martin-77/eurobox/cad/v110/SCAD/eurobox_v110_knob.scad

$fn=96;

pitch = 2.0;
female_core_r = 3.50;
female_major_r = 4.25;
female_root_w = 1.50;
female_crest_w = 0.90;

module ridge_rh(core_r, major_r, pitch, len, root_w, crest_w, z0=0, steps=480) {
    inner_r = core_r - 0.12;
    root_half = root_w/2;
    crest_half = crest_w/2;
    a1 = 360*len/pitch;
    function ang(i)=a1*i/steps;
    function zc(i)=pitch*ang(i)/360;
    function pt(r,a,z)=[r*cos(a),r*sin(a),z];
    pts=[for(i=[0:steps]) let(a=ang(i),z=zc(i))
        each [
            pt(inner_r,a,z-root_half),
            pt(major_r,a,z-crest_half),
            pt(major_r,a,z+crest_half),
            pt(inner_r,a,z+root_half)
        ]];
    side_faces=[for(i=[0:steps-1]) for(j=[0:3]) each [
        [4*(i+1)+((j+1)%4),4*(i+1)+j,4*i+j],
        [4*i+((j+1)%4),4*(i+1)+((j+1)%4),4*i+j]
    ]];
    start_face=[[2,1,0],[3,2,0]];
    e=4*steps;
    end_face=[[e+1,e+2,e+3],[e,e+1,e+3]];
    translate([0,0,z0])
        polyhedron(points=pts,faces=concat(side_faces,start_face,end_face),convexity=100);
}

module female_thread_cutter(len,z0=0,overrun=1.0) {
    union() {
        translate([0,0,z0-overrun])
            cylinder(r=female_core_r,h=len+2*overrun);
        ridge_rh(
            female_core_r,female_major_r,pitch,
            len+2*overrun,female_root_w,female_crest_w,
            z0-overrun,ceil((len+2*overrun)/pitch*16)
        );
    }
}

module scalloped_knob(h=9.5) {
    difference() {
        cylinder(r=15,h=h);
        for(a=[0:45:315])
            translate([16.2*cos(a),16.2*sin(a),-0.2])
                cylinder(r=3.4,h=h+0.4);
    }
}

knob_h = 9.50;
cone_h = 0.70;
cone_base_d = 11.20;
cone_tip_d = 8.30;

// Closed visible top:
// thread starts only above roof_z, leaving a solid cap.
roof_z = 1.60;
total_h = knob_h + cone_h;
thread_len = total_h - roof_z + 0.10;

difference() {
    union() {
        scalloped_knob(knob_h);

        // Male self-centering cone on clamp-facing side.
        // It bears on the rotating bushing recess, not the clamp.
        translate([0,0,knob_h])
            cylinder(d1=cone_base_d,d2=cone_tip_d,h=cone_h);
    }

    // Blind RH8x2 female thread: clamp-facing end open, visible end closed.
    female_thread_cutter(thread_len,roof_z,0.40);
}
