martin-77/eurobox/scripts/check_v60_workflow_contract.py

"""Post-build contract checks for the canonical v60 build.

This file only verifies the validation report produced by the canonical geometry
stages. It does not rebuild or independently substitute thread geometry.
"""

import json

with open('build_v60/VALIDATION_v60.json', encoding='utf-8') as fh:
    core = json.load(fh)
with open('build_v60/VALIDATION_v60_full.json', encoding='utf-8') as fh:
    full = json.load(fh)

assert not core['failures'], core['failures']
assert not full['failures'], full['failures']
assert core['stage'] == 'clean_structural_core_continuous_carrier', core['stage']
assert full['stage'] == 'full_direct_mechanism_v50_box_clamp_single_source', full['stage']

assert core['datums']['clamp_spacing_mm'] == 160.0
assert full['rack']['clamp_spacing_mm'] == 160.0
assert full['base']['right_bbox_mm'][0] <= 296.0
assert full['base']['right_bbox_mm'][1] <= 275.0
assert full['base']['mirror_delta_mm3'] <= 0.0001
assert full['handed_stl_export']['byte_distinct']
assert full['handed_stl_export']['mirror_geometry_ok']
assert full['handed_stl_export']['mirror_bounds_ok']
assert full['handed_stl_export']['mirror_vertex_set_ok']

# Box clamp: one v50-style architecture only. BASE is a smooth housing;
# the removable lead-nut cartridge contains the only working female RH8x2 thread.
box = full['box_clamp']
assert box['architecture'] == 'v50_direct_removable_lead_nut_cartridge_local_holm_stations', box
assert box['integral_female_threads'] is False, box
assert box['base_has_working_thread'] is False, box
assert box['working_female_thread_location'] == 'removable_lead_nut_cartridge', box
expected_spindles = core['datums']['box_clamp_spindle_x_mm']
assert box['spindle_x_mm'] == expected_spindles, box
assert abs(box['spindle_spacing_mm'] - (expected_spindles[1] - expected_spindles[0])) <= 1e-9, box
assert box['plate_x_mm'] == core['datums']['box_clamp_plate_x_mm'], box
assert box['plate_width_mm'] > 160.0, box
assert box['plate_travel_mm'] == 5.5, box
assert box['effective_total_width_mm'] <= 600.02, box
assert abs(box['spindle_z_mm'] - 24.54) <= 1e-9, box

lig = full['base']['carrier_spindle_ligaments']
assert lig['carrier_z0_mm'] == 9.54, lig
assert lig['carrier_z1_mm'] == 39.54, lig
assert abs(lig['lower_ligament_mm'] - lig['upper_ligament_mm']) <= 1e-9, lig
assert lig['lower_ligament_mm'] >= 9.0, lig

wall = full['base']['carrier_wall_material_checks']
assert len(wall) == 2, wall
for q in wall:
    assert q['corridor_centre_void'] is True, q
    assert [p['sample'] for p in q['samples']] == ['lower_outer','lower_inner','upper_inner','upper_outer'], q
    assert all(p['solid'] for p in q['samples']), q

station = full['base']['holm_station_checks']
assert len(station) == 2, station
assert all(abs(q['boss_to_holm_gap_mm'] - 24.0) <= 1e-9 for q in station), station
assert all(q['knob_to_holm_clearance_mm'] >= 20.0 for q in station), station

plate_lig = full['base']['plate_counterbore_ligaments']
assert abs(plate_lig['lower_ligament_mm'] - plate_lig['upper_ligament_mm']) <= 1e-9, plate_lig
assert plate_lig['lower_ligament_mm'] >= 9.0, plate_lig
assert len(box['cartridge_insertion']) == 10, box
assert all(q['base_common_mm3'] <= 0.0001 for q in box['cartridge_insertion']), box['cartridge_insertion']
assert set(q['lift_mm'] for q in box['cartridge_insertion']) == {20.0,10.0,5.0,2.0,0.0}, box['cartridge_insertion']

top_closure = full['base']['lead_nut_top_closure_checks']
assert len(top_closure) == 2, top_closure
for q in top_closure:
    assert abs(q['carrier_cap_top_z_mm'] - q['base_top_z_mm']) <= 1e-9, q
    assert len(q['samples']) == 9, q
    assert all(p['assembled_solid'] for p in q['samples']), q
    assert all(p['carrier_solid'] for p in q['samples']), q
    assert q['pin_recess_open'] is True, q
    assert 3.6 <= q['allowed_pin_recess_width_mm'] <= 4.0, q

guide_clear = full['base']['obsolete_guide_clearance_checks']
assert len(guide_clear) == 2, guide_clear
for q in guide_clear:
    assert len(q['samples']) == 2, q
    assert all(not p['solid'] for p in q['samples']), q

pin_cradles = full['base']['lead_nut_pin_wall_checks']
assert len(pin_cradles) == 2, pin_cradles
for q in pin_cradles:
    assert q['mode'] == 'round top-open U-cradle', q
    assert len(q['samples']) == 10, q
    for p in q['samples']:
        assert p['solid'] == p['expected_solid'], p

printability = box['lead_nut_printability']
assert printability['body_profile'] == 'true R8 lower semicircle', printability
assert abs(printability['semicircle_radius_mm'] - 8.0) <= 1e-9, printability
assert abs(printability['body_full_width_mm'] - 16.0) <= 1e-9, printability
assert printability['base_pocket_floor_bridge_mm'] <= 0.5, printability
assert printability['pin_cradle'] == 'round Ø3.4 top-open U-cradle', printability
assert printability['upper_body'] == 'closed except functional cross-pin bore/top-entry throat', printability
gap = printability['upper_gap_checks']
assert len(gap) == 6, gap
assert all(q['solid'] == q['expected_solid'] for q in gap), gap
assert {q['sample'] for q in gap if not q['solid']} == {'pin-axis','pin-top-entry'}, gap
assert printability['preferred_print_orientation'] == 'rotate -90deg about X; RH8x2 axis vertical', printability
span = printability['closing_span_samples']
assert [q['local_z_mm'] for q in span] == [0.0,-2.0,-4.0,-6.0,-8.0], span
assert all(span[i]['pocket_width_mm'] > span[i+1]['pocket_width_mm'] for i in range(len(span)-1)), span
assert span[-1]['pocket_width_mm'] <= 0.5, span

pin_drop = full['base']['lead_nut_pin_top_insertion']
assert len(pin_drop) == 2, pin_drop
assert all(abs(q['pin_axis_z_mm'] - 34.54) <= 1e-9 for q in pin_drop), pin_drop
for q in pin_drop:
    assert len(q['path']) == 5, q
    assert all(p['base_common_mm3'] <= 0.0001 for p in q['path']), q
    assert all(p['lead_nut_common_mm3'] <= 0.0001 for p in q['path']), q

assert box['final_assembly_replaceable_module_count'] == 0, box
assert box['final_assembly_contains_separate_lead_nut_hardware'] is True, box
assert box['final_assembly_lead_nut_cartridge_count'] == 4, box
assert box['final_assembly_lead_nut_pin_count'] == 4, box
assert box['final_assembly_lead_nut_clip_count'] == 4, box
assert box['final_assembly_box_clamp_knob_count'] == 4, box
assert box['final_assembly_knob_retainer_count'] == 4, box
assert box['final_assembly_plate_retainer_clip_count'] == 4, box
assert box['final_assembly_installed_spindle_x_mm'] == expected_spindles, box
assert all(q['base_common_mm3'] <= 0.0001 for q in box['thread_motion']), box['thread_motion']
assert box['thread_brep_common_tolerance_mm3'] == 1.20, box
assert all(q['cartridge_common_mm3'] <= box['thread_brep_common_tolerance_mm3'] for q in box['thread_motion']), box['thread_motion']

# Lead screw must be the exact closed printable CGAL mesh. The 7 mm knob
# drive now starts with a support-free hex frustum and retains 5 mm full AF10.
ls = box['lead_screw']
assert ls['knob_hex_length_mm'] == ls['knob_thickness_mm'] == 7.0, ls
assert ls['full_hex_drive_length_mm'] >= 5.0, ls
assert abs(ls['hex_taper_length_mm'] - 2.0) <= 1e-9, ls
assert ls['mesh_topology']['boundary_edges'] == 0, ls
assert ls['mesh_topology']['nonmanifold_edges'] == 0, ls
assert len(ls['main_thread_samples']) == 8, ls
assert all(q['ridge_center_solid'] for q in ls['main_thread_samples']), ls
assert all(not q['between_turns_solid'] for q in ls['main_thread_samples']), ls

lsp = box['lead_screw_printability']
assert lsp['preferred_print_orientation'] == 'vertical on outer-stud pilot; screw axis +Z', lsp
assert abs(lsp['flat_pilot_d_mm'] - 6.5) <= 1e-9, lsp
assert abs(lsp['flat_pilot_h_mm'] - 0.8) <= 1e-9, lsp
assert lsp['outer_thread_usable_mm'] >= 6.0, lsp
assert abs(lsp['hex_taper_h_mm'] - 2.0) <= 1e-9, lsp
assert lsp['full_hex_drive_h_mm'] >= 5.0, lsp
assert lsp['shoulder_taper_max_slope_dr_dz'] <= 1.0, lsp
assert lsp['plate_matching_conical_seat'] is True, lsp
assert lsp['knob_matching_hex_frustum'] is True, lsp

pr = box['plate_spindle_retention']
assert pr['clip_count_final_assembly'] == 4, pr
assert len(pr['checks']) == 2, pr
assert all(q['spindle_common_mm3'] <= 0.0001 for q in pr['checks']), pr
assert all(q['plate_common_mm3'] <= 0.0001 for q in pr['checks']), pr
assert pr['service_channel_width_mm'] >= 11.2, pr
assert pr['service_channel_depth_mm'] == 2.0, pr
assert len(pr['clip_insertion_path']) == 10, pr
assert all(q['plate_common_mm3'] <= 0.00001 for q in pr['clip_insertion_path']), pr

ms = box['mounting_sequence']
assert ms['order'] == [
    'lead_nut_insert_from_top',
    'lead_nut_cross_pin',
    'lead_nut_pin_clip',
    'lead_screw_through_plate',
    'plate_retainer_clip_via_bottom_service_channel',
    'plate_spindle_subassembly_threaded_into_fixed_lead_nut',
    'knob_on_tapered_7mm_hex_with_5mm_full_drive',
    'knob_retainer_nut_on_outer_RH8x2_stud',
], ms
assert len(ms['lead_nut_top_insertion']) == 10, ms
assert all(q['base_common_mm3'] <= 0.0001 for q in ms['lead_nut_top_insertion']), ms
assert len(ms['lead_nut_pin_top_insertion']) == 2, ms
for q in ms['lead_nut_pin_top_insertion']:
    assert len(q['path']) == 5, q
    assert all(p['base_common_mm3'] <= 0.0001 for p in q['path']), q
    assert all(p['lead_nut_common_mm3'] <= 0.0001 for p in q['path']), q
assert len(ms['threaded_plate_approach']) == 10, ms
assert all(q['plate_base_common_mm3'] <= 0.0001 for q in ms['threaded_plate_approach']), ms
assert all(q['spindle_base_common_mm3'] <= 0.0001 for q in ms['threaded_plate_approach']), ms
assert all(q['spindle_lead_nut_common_mm3'] <= box['thread_brep_common_tolerance_mm3'] for q in ms['threaded_plate_approach']), ms
assert all(q['knob_base_common_mm3'] <= 0.0001 for q in ms['threaded_plate_approach']), ms
assert all(q['knob_retainer_base_common_mm3'] <= 0.0001 for q in ms['threaded_plate_approach']), ms
assert len(ms['operating_knob_clearance']) == 14, ms
assert all(q['knob_base_common_mm3'] <= 0.0001 for q in ms['operating_knob_clearance']), ms
assert all(q['retainer_base_common_mm3'] <= 0.0001 for q in ms['operating_knob_clearance']), ms

# The removable lead-nut wear cartridge must contain a real printable RH8x2
# female helix.  Direct final-part samples prevent a smooth cylindrical bore
# from ever satisfying the workflow contract again.
ln = box['lead_nut_thread']
assert ln['standard'] == 'RH8x2 true radial/axial printable matched pair', ln
assert ln['pitch_mm'] == 2.0, ln
assert ln['male_major_d_mm'] == 8.0, ln
assert ln['male_crest_width_mm'] >= 0.50, ln
assert ln['female_crest_material_between_turns_mm'] >= 0.45, ln
assert ln['radial_thread_engagement_mm'] >= 0.40, ln
assert len(ln['samples']) == 8, ln
assert all(not q['groove_center_solid'] for q in ln['samples']), ln
assert all(q['between_turns_solid'] for q in ln['samples']), ln
assert ln['validated_export_part'] == 'eurobox_v60_lead_nut', ln

# The separate box-clamp knob retainer must contain a real printable RH8x2
# female helix, matched to the actual outer stud on the exported lead screw.
kr = box['knob_retainer_thread']
assert kr['standard'] == 'RH8x2 true radial/axial printable pair', kr
assert kr['pitch_mm'] == 2.0, kr
assert kr['male_major_d_mm'] == 8.0, kr
assert kr['male_crest_width_mm'] >= 0.50, kr
assert kr['female_crest_material_between_turns_mm'] >= 0.45, kr
assert kr['radial_core_clearance_mm'] >= 0.20, kr
assert kr['radial_major_clearance_mm'] >= 0.20, kr
assert len(kr['samples']) == 4, kr
assert all(q['male_ridge_center_solid'] for q in kr['samples']), kr
assert all(not q['male_between_turns_solid'] for q in kr['samples']), kr
assert all(not q['female_groove_center_solid'] for q in kr['samples']), kr
assert all(q['female_between_turns_solid'] for q in kr['samples']), kr
assert kr['validated_export_part'] == 'eurobox_v60_knob_retainer_nut', kr

# Rack retainer: one final printable 12x3 pair only.  The contract checks the
# actual radial/axial profile dimensions and direct point samples from the final
# BASE/retainer, rather than expensive whole-body phase booleans.
rlp = full['rack']['lower_printability']
assert rlp['mechanical_geometry'] == 'proven Lower shell unchanged; closure tongue extended downward only', rlp
assert rlp['print_orientation'] == 'natural Z-up on common shell/tongue floor', rlp
assert abs(rlp['common_floor_z_mm'] + 14.5) <= 1e-9, rlp
assert rlp['common_floor_material_fraction'] >= 0.995, rlp
assert rlp['saddle_under_material_mm'] >= 8.3, rlp
assert rlp['rack_saddle'] == 'upward-open semicircular seat', rlp
assert rlp['pivot_pin_bore'] == 'small horizontal round self-closing opening', rlp
pf = rlp['pivot_print_feet']
assert pf['z_mm'] == [-14.5,-10.3], pf
assert pf['y_mm'] == [-17.0,-4.0], pf
assert abs(pf['ear_thickness_mm'] - 4.6) <= 1e-9, pf
assert rlp['m4_clearance'] == 'vertical', rlp
assert abs(rlp['m4_clearance_d_mm'] - 5.0) <= 1e-9, rlp
assert rlp['functional_round_pivot_bore_preserved'] is True, rlp

closure = full['rack']['m4_closure']
assert closure['carrier_bottom_plane_z_mm'] == 9.54, closure
assert closure['carrier_top_plane_z_mm'] == 39.54, closure
assert closure['lower_closure_thickness_mm'] == 13.0, closure
assert closure['lower_closure_z_mm'] == [-14.5,-1.5], closure
assert closure['lower_shell_floor_z_mm'] == -14.5, closure
assert closure['lower_saddle_under_material_mm'] >= 8.3, closure
assert closure['upper_nut_pocket_af_mm'] == 6.9, closure
assert closure['upper_nut_pocket_z_mm'] == [5.4,9.0], closure
assert closure['upper_nut_floor_z_mm'] == 3.4, closure
assert closure['upper_nut_floor_thickness_mm'] >= 2.0, closure
assert closure['upper_nut_floor_screw_clear_d_mm'] <= 4.6, closure
assert closure['upper_nut_floor_radial_ligament_mm'] >= 1.15, closure
assert closure['upper_nut_floor_material_fraction'] >= 0.985, closure
assert closure['knob_plastic_web_mm'] == 3.2, closure
assert closure['usable_screw_length_above_knob_mm'] == 23.6, closure
assert closure['calculated_screw_tip_z_mm'] == 9.1, closure
assert closure['full_nut_screw_overrun_margin_mm'] >= 0.49, closure
assert closure['screw_length_mm'] == 30.0, closure
assert closure['retainer_pitch_mm'] == 3.0, closure
assert closure['retainer_length_mm'] >= 28.0, closure
assert closure['retainer_male_major_d_mm'] == 12.0, closure
assert closure['retainer_female_major_d_mm'] >= 12.5, closure
assert closure['retainer_thread_profile_generator'] == 'true_radial_axial_OCC_fused', closure
assert closure['entry_clear_d_mm'] >= closure['retainer_male_major_d_mm'] + 0.8, closure
assert 0.35 <= closure['entry_clear_depth_mm'] <= 0.60, closure
assert closure['female_thread_start_recess_mm'] <= 0.60, closure
assert len(closure['female_thread_removed_mm3']) == 2, closure
assert all(v >= 8.0 for v in closure['female_thread_removed_mm3']), closure
assert closure['lower_transition_shape'] == 'shallow_conical_flare', closure
assert closure['lower_transition_z_mm'] == [9.0,11.0], closure
assert closure['lower_transition_d_mm'] == [8.1,10.5], closure

ltw = closure['lower_transition_witness']
assert len(ltw) == 2, ltw
for q in ltw:
    assert len(q['samples']) == 3, q
    assert all(not s['inner_probe_solid'] for s in q['samples']), q
    assert all(s['outer_probe_solid'] for s in q['samples']), q

nhw = closure['nut_hex_capture_witness']
assert len(nhw) == 2, nhw
for q in nhw:
    assert len(q['samples']) == 3, q
    assert all(s['inner_hex_point_void'] for s in q['samples']), q
    assert all(s['outer_flat_wall_solid'] for s in q['samples']), q

p = closure['thread_printability']
assert p['pitch_mm'] == 3.0, p
assert p['male_crest_width_mm'] >= 0.70, p
assert p['female_crest_material_between_turns_mm'] >= 0.80, p
assert 9.0 <= p['approx_full_turns'] <= 10.0, p
assert p['radial_core_clearance_mm'] >= 0.20, p
assert p['radial_major_clearance_mm'] >= 0.20, p
assert p['axial_root_clearance_mm'] >= 0.25, p
assert p['axial_crest_clearance_mm'] >= 0.25, p
assert p['target_nozzle_mm'] == 0.4, p
mn = p['male_nose_transition']
assert mn['shape'] == 'shallow_conical_flare', mn
assert mn['z_local_mm'] == [-2.0,0.0], mn
assert mn['diameter_mm'] == [7.6,10.0], mn
assert abs(mn['radial_per_vertical_slope'] - 0.6) <= 1e-9, mn
lt = p['lower_transition']
assert lt['shape'] == 'shallow_conical_flare', lt
assert lt['z_mm'] == [9.0,11.0], lt
assert lt['diameter_mm'] == [8.1,10.5], lt
assert abs(lt['height_mm'] - 2.0) <= 1e-9, lt
assert abs(lt['radial_per_vertical_slope'] - 0.6) <= 1e-9, lt
assert abs(lt['female_cylindrical_bore_starts_z_mm'] - 11.0) <= 1e-9, lt

mouth = closure['female_helical_witness']
assert len(mouth) == 2, mouth
assert all(q['blocked_sample_points'] == 0 for q in mouth), mouth

female_samples = closure['female_thread_point_samples']
assert len(female_samples) == 16, female_samples
assert all(not q['groove_center_solid'] for q in female_samples), female_samples
assert all(q['between_turns_solid'] for q in female_samples), female_samples

male_samples = closure['male_thread_point_samples']
assert len(male_samples) == 8, male_samples
assert all(q['ridge_center_solid'] for q in male_samples), male_samples
assert all(not q['between_turns_solid'] for q in male_samples), male_samples

cc = core['geometry']['continuous_carrier']
assert cc['material_fraction'] >= 0.995, cc
assert cc['rack_tube_common_mm3'] <= 0.0001, cc
# Front holm no longer overlaps the carrier directly; the intentional load
# path is carrier -> full-depth straight root -> holm.
assert cc['front_holm_direct_carrier_common_mm3'] <= 0.000001, cc
assert cc['rear_holm_common_mm3'] >= 100.0, cc
assert cc['backstop_common_mm3'] >= 100.0, cc
fr = cc['front_holm_root_tie']
assert fr['section'] == 'full_carrier_depth_straight_hollow_root_with_side_twin_and_center_webs', fr
assert fr['x_mm'] == [-96.0,-64.0], fr
assert fr['carrier_y_mm'] == [-8.0,26.0], fr
assert abs(fr['carrier_depth_mm'] - 34.0) <= 1e-9, fr
assert fr['y_mm'] == [-8.0,36.0], fr
assert abs(fr['carrier_engagement_mm'] - 34.0) <= 1e-9, fr
assert abs(fr['straight_after_carrier_mm'] - 10.0) <= 1e-9, fr
assert abs(fr['normal_holm_start_y_mm'] - 35.6) <= 1e-9, fr
assert fr['holm_splice_common_mm3'] >= 150.0, fr
assert fr['material_fraction'] >= 0.995, fr
assert fr['carrier_common_mm3'] >= 8000.0, fr
assert fr['green_drop_excluded_from_root_zone'] is True, fr
assert abs(fr['green_drop_x_min_mm'] + 64.0) <= 1e-9, fr
assert len(fr['hollow_cell_checks']) == 4, fr
assert all(not q['solid'] for q in fr['hollow_cell_checks']), fr
assert fr['x_z_envelope_growth_mm'] == [0.0,0.0], fr
bd = cc['backstop_base_drop']
assert bd['profile'] == 'filled_quarter_ellipse_tapered_to_stop_bottom', bd
assert bd['x_edge_inset_mm'] == 3.0, bd
assert bd['closed_solid'] is True, bd
assert abs(bd['tip_width_mm'] - 1.2) <= 1e-9, bd
assert bd['z_root_tip_mm'][1] <= -41.8 + 1e-9, bd
assert bd['material_fraction'] >= 0.995, bd
assert bd['panel_common_mm3'] >= 5.0, bd
assert bd['carrier_common_mm3'] >= 5.0, bd
assert bd['rack_tube_common_mm3'] <= 0.0001, bd
assert bd['z_root_tip_mm'][0] > bd['z_root_tip_mm'][1], bd
assert bd['y_root_tip_mm'][0] > bd['y_root_tip_mm'][1], bd
assert cc['section'] == 'fully_closed_box_with_internal_saddle_web', cc
assert abs(cc['end_wall_thickness_mm'] - 3.2) <= 1e-9, cc
assert set(cc['end_wall_material_fractions']) == {'x0','x1'}, cc
assert all(v >= 0.999 for v in cc['end_wall_material_fractions'].values()), cc

gd = cc['green_shelf_drop']
assert gd['target'] == 'green lower carrier shelf between saddle web +Y face and outer +Y wall', gd
assert gd['root_side'] == 'internal saddle web at Y=7', gd
assert gd['tip_side'] == 'outer +Y side wall inner face at Y=22.8', gd
assert gd['x_mm'][0] == -64.0, gd
assert gd['excluded_front_root_x_mm'] == [-96.0,-64.0], gd
assert gd['y_mm'] == [7.0, 22.8], gd
assert abs(gd['span_mm'] - 15.8) <= 1e-6, gd
assert abs(gd['shelf_z_mm'] - 14.04) <= 1e-6, gd
assert abs(gd['root_z_mm'] - 29.84) <= 1e-6, gd
assert gd['centre_witness_material_fraction'] >= 0.999, gd
assert gd['rack_closure_y_mm'] == 11.0, gd

gh = core['geometry']['inner_green_shelf_support']
assert gh['target'] == 'central lower long-holm flange between twin webs', gh
assert gh['print_orientation'] == 'BASE upside-down; installed high-Z prints first', gh
assert len(gh['checks']) == 2, gh
for q in gh['checks']:
    assert len(q['inner_haunch_material_fractions']) == 2, q
    assert all(v >= 0.995 for v in q['inner_haunch_material_fractions']), q
    assert len(q['above_flange_point_states']) == 5, q
    assert all(p['solid'] for p in q['above_flange_point_states']), q
    assert q['web_overlap_mm'] == 0.2, q
    assert q['flange_overlap_mm'] == 0.2, q
    assert q['centre_overlap_each_side_mm'] == 0.2, q
    assert q['rise_mm'] == 10.0, q

rear_junctions = core['geometry']['crosshead_rear_holm_junctions']
assert len(rear_junctions) == 2, rear_junctions
assert {q['holm'] for q in rear_junctions} == {'front_holm','rear_holm'}, rear_junctions
for q in rear_junctions:
    assert q['front_y0_web_material_fraction'] >= 0.999, q
    assert q['rear_y1_wall_material_fraction'] >= 0.999, q
    assert q['straight_holm_tail_material_fraction'] >= 0.999, q
    assert q['straight_tail_y_mm'][0] < core['geometry']['crosshead_print_support']['crosshead_y_mm'][0], q
    assert abs(q['straight_tail_y_mm'][1] - 220.0) <= 1e-9, q
    assert abs(q['rear_open_span_mm'] - 5.685) <= 1e-3, q
    assert q['legacy_haunch_residual_mm3'] <= 0.0001, q
    assert len(q['hollow_cell_probes']) == 4, q
    assert all(not p['solid'] for p in q['hollow_cell_probes']), q

ch = core['geometry']['crosshead_print_support']
assert ch['strategy'] == 'original front/Y0 web retained; holm-zone DROP removed; missing rear/Y1 wall added; long holm is straight hollow multi-web from crosshead through head root', ch
assert len(ch['crosshead_y_mm']) == 2, ch
plate_sweep_y0 = core['datums']['plate_sweep_xyz_mm'][1][0]
assert abs(ch['crosshead_y_mm'][1] - (plate_sweep_y0 - 0.2)) <= 1e-6, ch
assert ch['central_drop_material_fraction'] >= 0.995, ch
assert abs(ch['end_wall_thickness_mm'] - 3.2) <= 1e-9, ch
assert len(ch['end_wall_checks']) == 2, ch
assert {q['end'] for q in ch['end_wall_checks']} == {'x0','x1'}, ch
assert all(q['material_fraction'] >= 0.999 for q in ch['end_wall_checks']), ch
assert len(ch['checks']) == 5, ch
for q in ch['checks']:
    assert [p['sample'] for p in q['samples']] == ['bottom', 'web', 'top'], q
    assert all(p['solid'] for p in q['samples']), q

hh = core['geometry']['holm_head_closures']
assert len(hh) == 2, hh
for q in hh:
    assert abs(q['central_head_fill_width_mm'] - 25.6) <= 1e-9, q
    assert q['cap_fraction'] >= 0.999, q
    assert len(q['drop_fractions']) == 3, q
    assert all(v >= 0.999 for v in q['drop_fractions']), q
    assert q['central_head_probe_material_fraction'] >= 0.999, q

cage_checks = {q['name']: q for q in full['base']['cage_reinforcement_checks']}
for name in ('cross_bottom_inner_drop_rear','cross_bottom_inner_drop_front'):
    assert name in cage_checks, cage_checks
    assert cage_checks[name]['material_fraction'] >= 0.990, cage_checks[name]

checks = full['installed_support_orientation']['checks']
assert len(checks) == 2
for q in checks:
    assert q['right_outward_extent_mm'] >= 210.0, q
    assert q['left_outward_extent_mm'] >= 210.0, q
    assert q['right_inward_extent_mm'] <= 30.0, q
    assert q['left_inward_extent_mm'] <= 30.0, q

print('V60_WORKFLOW_CONTRACT canonical single-source geometry checks passed', flush=True)
