martin-77/eurobox/scripts/apply_v50_rack_root_reinforcement.py

from pathlib import Path
import re

p = Path('scripts/build_v50.py')
s = p.read_text(encoding='utf-8')
orig = s

# Carry the normal longitudinal I-beam section all the way to the front edge
# of each fixed rack-clamp station. Keep the proven saddle/pivot datums, but use
# substantially thicker fixed clevis cheeks around the rack-lower pivot. The
# moving lower jaw remains 25.2 mm wide with 0.8 mm total running clearance.
pattern = re.compile(r"def make_upper_station\(xc\):\n.*?\n\nbase_parts =", re.S)
replacement = '''RACK_FIXED_LUG_T = 6.0
RACK_FIXED_LUG_INNER_X = 13.0
RACK_FIXED_LUG_OUTER_X = RACK_FIXED_LUG_INNER_X + RACK_FIXED_LUG_T

def make_upper_station(xc):
    bridge = box(xc-RACK_FIXED_LUG_OUTER_X, -8.0, 0.0,
                 2*RACK_FIXED_LUG_OUTER_X, 22.0, 16.0)

    root_beam = make_i_beam_y(xc, -8.0, 36.0)

    # 6 mm fixed clevis lugs, grown OUTWARD so the proven 26.0 mm inner gap and
    # the lower-jaw running clearance are unchanged. The old 4 mm cheeks were
    # too fragile for PETG around a 4.6 mm pin bore.
    lug_l = cyl_x(7.0, RACK_FIXED_LUG_T,
                  xc-RACK_FIXED_LUG_OUTER_X, PIN_Y, PIN_Z)
    lug_r = cyl_x(7.0, RACK_FIXED_LUG_T,
                  xc+RACK_FIXED_LUG_INNER_X, PIN_Y, PIN_Z)
    web_l = box(xc-RACK_FIXED_LUG_OUTER_X, PIN_Y, PIN_Z,
                RACK_FIXED_LUG_T, 8.0, 7.0)
    web_r = box(xc+RACK_FIXED_LUG_INNER_X, PIN_Y, PIN_Z,
                RACK_FIXED_LUG_T, 8.0, 7.0)
    cheek_l = box(xc-RACK_FIXED_LUG_OUTER_X, -8.0, -7.0,
                  RACK_FIXED_LUG_T, 9.0, 7.0)
    cheek_r = box(xc+RACK_FIXED_LUG_INNER_X, -8.0, -7.0,
                  RACK_FIXED_LUG_T, 9.0, 7.0)

    s = fuse_all([bridge, root_beam,
                  lug_l, lug_r, web_l, web_r, cheek_l, cheek_r])
    # Keep these two canonical cut lines compatible with the later rack-lock
    # pass; the 40 mm cutter fully spans the reinforced +/-19 mm station.
    s = s.cut(cyl_x(UPPER_SADDLE_R, 40.0, xc-20.0, 0.0, 0.0))
    s = s.cut(cyl_x(PIN_HOLE_D/2, 40.0, xc-20.0, PIN_Y, PIN_Z))
    return s.removeSplitter()

base_parts ='''
s, n = pattern.subn(replacement, s, count=1)
assert n == 1, 'upper station block not found'

# The original pin was sized for the former 4 mm cheeks. Growing both fixed
# cheeks outward to 6 mm would bury the head by 0.6 mm and leave the C-clip
# groove inside the right cheek. Keep the frozen pivot and shaft diameter, but
# lengthen the service pin so the head has 0.8 mm external clearance and the
# clip groove starts 1.0 mm beyond the reinforced right cheek.
pin_pattern = re.compile(
    r"PIN = fuse_all\(\[\n"
    r"\s*cyl_x\(2\.0, 33\.5, -18\.4, 0, 0\),\n"
    r"\s*cyl_x\(1\.55, 1\.5, 15\.1, 0, 0\),\n"
    r"\s*cyl_x\(2\.0, 1\.7, 16\.6, 0, 0\),\n"
    r"\s*cyl_x\(3\.75, 2\.4, -20\.8, 0, 0\),\n"
    r"\]\)", re.S)
pin_replacement = '''PIN = fuse_all([
    # Main 4.0 mm shaft: from 0.8 mm outside the left 6 mm cheek through to
    # 1.0 mm outside the right cheek, where the retaining groove begins.
    cyl_x(2.0, 39.8, -19.8, 0, 0),
    # C-clip groove and retaining end are fully outside the +19 mm cheek face.
    cyl_x(1.55, 1.5, 20.0, 0, 0),
    cyl_x(2.0, 1.7, 21.5, 0, 0),
    # Head inner face at -19.8 mm -> 0.8 mm clear of the -19 mm cheek face.
    cyl_x(3.75, 2.4, -22.2, 0, 0),
])'''
s, pn = pin_pattern.subn(pin_replacement, s, count=1)
assert pn == 1, 'rack pin block not found for reinforced-clevis length correction'

anchor = "V['beam_sanity'] = {\n"
assert anchor in s
insert = '''root_area = 2*ARM_W*FLANGE_T + 2*WEB_T*(ARM_H-2*FLANGE_T)
root_Ix = 2*(ARM_W*FLANGE_T**3/12.0 + ARM_W*FLANGE_T*(ARM_H/2.0-FLANGE_T/2.0)**2) \\
          + 2*(WEB_T*(ARM_H-2*FLANGE_T)**3/12.0)
root_static_stress = F_arm * L_check * (ARM_H/2.0) / root_Ix
V['rack_root_strengthening'] = {
    'design': 'continuous_same_I_beam_as_long_arm_plus_6mm_fixed_clevis',
    'front_edge_y_mm': -8.0,
    'root_beam_start_y_mm': -8.0,
    'root_beam_end_y_mm': 36.0,
    'regular_arm_start_y_mm': ARM_Y0,
    'root_to_regular_arm_overlap_y_mm': 36.0-ARM_Y0,
    'bridge_start_y_mm': -8.0,
    'bridge_end_y_mm': 14.0,
    'bridge_to_root_beam_overlap_y_mm': 22.0,
    'tube_clearance_preserved_by_post_fuse_saddle_cut': True,
    'fixed_clevis_lug_thickness_mm': RACK_FIXED_LUG_T,
    'fixed_clevis_inner_gap_mm': 2*RACK_FIXED_LUG_INNER_X,
    'moving_lower_width_mm': 25.2,
    'total_lateral_running_clearance_mm': 2*RACK_FIXED_LUG_INNER_X-25.2,
    'rack_pin_head_clearance_from_left_cheek_mm': 0.8,
    'rack_pin_clip_groove_clearance_from_right_cheek_mm': 1.0,
    'root_section_area_mm2': round(root_area, 3),
    'root_section_Ix_mm4': round(root_Ix, 3),
    'static_root_stress_mpa_at_existing_16kg_assumption': round(root_static_stress, 4),
    'dynamic_3x_root_stress_mpa_at_existing_16kg_assumption': round(3*root_static_stress, 4),
}

'''
s = s.replace(anchor, insert + anchor, 1)

fail_anchor = "failures = []\n"
assert fail_anchor in s
fail_insert = '''r = V['rack_root_strengthening']
if abs(r['root_beam_start_y_mm'] - r['front_edge_y_mm']) > 1e-9:
    failures.append('Rack root I-beam no longer reaches fixed-station front edge')
if r['bridge_to_root_beam_overlap_y_mm'] < 20.0:
    failures.append('Rack clamp bridge/root-beam overlap below design minimum')
if r['root_to_regular_arm_overlap_y_mm'] < 10.0:
    failures.append('Rack root/regular-arm overlap below design minimum')
if r['fixed_clevis_lug_thickness_mm'] < 6.0:
    failures.append('Rack lower fixed clevis support below 6 mm PETG minimum')
if not (0.6 <= r['total_lateral_running_clearance_mm'] <= 1.2):
    failures.append('Rack lower clevis running clearance outside 0.6..1.2 mm')
if r['rack_pin_head_clearance_from_left_cheek_mm'] < 0.6:
    failures.append('Rack pin head clearance is too small for PETG service fit')
if r['rack_pin_clip_groove_clearance_from_right_cheek_mm'] < 0.8:
    failures.append('Rack pin C-clip groove is not fully outside reinforced clevis')
if abs(r['root_section_area_mm2'] - 422.4) > 1e-3:
    failures.append('Rack root section area no longer matches normal arm')
if abs(r['root_section_Ix_mm4'] - 52243.2) > 1e-3:
    failures.append('Rack root section inertia no longer matches normal arm')
'''
s = s.replace(fail_anchor, fail_anchor + fail_insert, 1)

assert s != orig
p.write_text(s, encoding='utf-8')
print('Applied v50 rack-root reinforcement: proven I-beam root + 6 mm fixed clevis cheeks + serviceable longer pin')
