martin-77/eurobox/scripts/build_v60_full.py

"""Canonical v60 full mechanism builder.

Production order:
1. structural full baseline;
2. phase-matched RH8x2 cartridge prerequisite;
3. clean side-style v60 front with two replaceable clamp cassettes;
4. spindle-envelope-clear wear cartridge + open handle/knob-retainer access;
5. M4x30 rack closure;
6. explicit printable 12x2 rack-retainer thread pair;
7. hard audit of every final service thread and threaded access path;
8. lightweight final inspection assembly.

Each stage emits V60_TIMING records into build_v60/TIMING_v60.json so later
runtime/cost work can target measured hotspots instead of guessing.
"""

from v60_timing import start_timer, stop_timer

_t = start_timer('full.import_structural_baseline')
from build_v60_full_baseline import *  # noqa: F401,F403,E402
stop_timer('full.import_structural_baseline', _t)

# The structural baseline is now also the single canonical box-clamp builder.
# It owns the v50-style removable RH8x2 cartridge, pin/clip and moving hardware.
# No prerequisite/front-rebuild stages are allowed after this point.
RIGHT_FULL = RIGHT_FULL
LEFT_FULL = LEFT_FULL
PLATE = PLATE
SPINDLE_X = SPINDLE_X
LEAD_NUT = LEAD_NUT
NUT_PIN = NUT_PIN
NUT_PIN_CLIP = NUT_PIN_CLIP
LEAD_NUT_PIN_LOCAL_Y = LEAD_NUT_PIN_LOCAL_Y
LEAD_NUT_PIN_LOCAL_Z = LEAD_NUT_PIN_LOCAL_Z
NUT_PIN_CLIP_X = NUT_PIN_CLIP_X
PIN_Y_BOX_CLAMP = NUT_Y0 + LEAD_NUT_PIN_LOCAL_Y
PIN_Z_BOX_CLAMP = SPINDLE_Z + LEAD_NUT_PIN_LOCAL_Z
BOX_CLAMP_KNOB = KNOB
BOX_CLAMP_CAP_NUT = CAP_NUT
BOX_CLAMP_KNOB_Y_LOCAL = -(SPINDLE_LOCAL_JOURNAL + SPINDLE_LOCAL_SHOULDER + LEAD_THREAD_LEN)
BOX_CLAMP_CAP_Y_LOCAL = BOX_CLAMP_KNOB_Y_LOCAL - KNOB.BoundBox.YLength

# Rack closure consumes the canonical front through this partially initialized
# module, so the variables above must be assigned first.
_t = start_timer('full.apply_rack_closure')
import apply_v60_rack_closure as _rack_closure  # noqa: E402
stop_timer('full.apply_rack_closure', _t)

RIGHT_FULL = _rack_closure.RIGHT
LEFT_FULL = _rack_closure.LEFT
LOWER = _rack_closure.LOWER
RACK_HAND_KNOB = _rack_closure.RACK_HAND_KNOB

_t = start_timer('full.apply_final_retainer_thread')
import apply_v60_retainer_thread_final as _retainer_final  # noqa: E402
stop_timer('full.apply_final_retainer_thread', _t)

RIGHT_FULL = _retainer_final.RIGHT
LEFT_FULL = _retainer_final.LEFT
RACK_NUT_RETAINER = _retainer_final.RACK_NUT_RETAINER

RACK_M4_SCREW_LENGTH = _rack_closure.RACK_SCREW_LENGTH
RACK_M4_LOWER_CLEAR_D = _rack_closure.LOWER_CLEAR_D
RACK_M4_NUT_AF = _rack_closure.RACK_NUT_AF
RACK_M4_NUT_H = _rack_closure.RACK_NUT_H
RACK_M4_NUT_Z0 = _rack_closure.RACK_NUT_Z0
RACK_RETAINER_PITCH = _retainer_final.PITCH
RACK_RETAINER_BORE_D = _rack_closure.RETAINER_BORE_D
RACK_RETAINER_MALE_MAJOR_D = 2.0 * _retainer_final.MALE_MAJOR_R
RACK_RETAINER_FEMALE_MAJOR_D = 2.0 * _retainer_final.FEMALE_MAJOR_R
RACK_LOWER_CLOSURE_THICKNESS = _rack_closure.LOWER_PAD_Z1 - _rack_closure.LOWER_PAD_Z0

_t = start_timer('full.build_lightweight_final_assembly')
import apply_v60_final_assembly as _final_assembly  # noqa: F401,E402
stop_timer('full.build_lightweight_final_assembly', _t)

print(
    'V60_STAGE canonical v50-style direct box clamp + single-source rack retainer thread active',
    flush=True,
)
